YannickR26/ESP-Power-Monitoring/Software/src/HttpServer.cpp

#include <littleFS.h>
#include <ESP8266mDNS.h>
#include <ESP8266HTTPUpdateServer.h>

// You can update by 'curl -F "image=@firmware.bin" ESP_Monitoring.local/'

#include "WiFiManager.h"
#include "HttpServer.h"
#include "ATM90E32.h"
#include "Logger.h"
#include "Mqtt.h"

/********************************************************/
/******************** Public Method *********************/
/********************************************************/

HttpServer::HttpServer()
    : _webServer(80), _httpUpdater(true)
{
}

HttpServer::~HttpServer()
{
}

void HttpServer::setup(void)
{
  MDNS.begin(Configuration._hostname.c_str());
  MDNS.addService("http", "tcp", 80);

  _ftpServer.begin(Configuration._hostname, Configuration._hostname);
  MDNS.addService("ftp", "tcp", 21);

  _webServer.on("/restart", [&]() {
    _webServer.send(200, "text/plain", "ESP restart now !");
    delay(200);
    ESP.restart();
  });

  _webServer.on("/wifimanager", [&]() {
    _webServer.send(200, "text/plain", "Reset WifiManager configuration, restart now in AP mode...");
    delay(200);
    WiFiManager wifiManager;
    wifiManager.resetSettings();
    delay(200);
    ESP.restart();
  });

  _webServer.on("/config", HTTP_GET, HttpServer::getConfig);
  _webServer.on("/config", HTTP_POST, HttpServer::setConfig);
  _webServer.on("/status", HTTP_GET, HttpServer::getStatus);
  _webServer.on("/set", HttpServer::handleSet);

  _webServer.onNotFound(HttpServer::handleNotFound);

  _httpUpdater.setup(&_webServer, String("/update"));
  _webServer.begin();
}

void HttpServer::handle(void)
{
  _webServer.handleClient();
  MDNS.update();
  _ftpServer.handleFTP();
}

String HttpServer::getContentType(String filename)
{
  if (HTTPServer.webServer().hasArg("download"))
    return "application/octet-stream";
  else if (filename.endsWith(".htm"))
    return "text/html";
  else if (filename.endsWith(".html"))
    return "text/html";
  else if (filename.endsWith(".css"))
    return "text/css";
  else if (filename.endsWith(".js"))
    return "application/javascript";
  else if (filename.endsWith(".png"))
    return "image/png";
  else if (filename.endsWith(".gif"))
    return "image/gif";
  else if (filename.endsWith(".jpg"))
    return "image/jpeg";
  else if (filename.endsWith(".ico"))
    return "image/x-icon";
  else if (filename.endsWith(".xml"))
    return "text/xml";
  else if (filename.endsWith(".pdf"))
    return "application/x-pdf";
  else if (filename.endsWith(".zip"))
    return "application/x-zip";
  else if (filename.endsWith(".gz"))
    return "application/x-gzip";
  return "text/plain";
}

// send the right file to the client (if it exists)
bool HttpServer::handleFileRead(String path)
{
  Log.println("handleFileRead: " + path);
  if (path.endsWith("/"))
  {
    path += "index.html"; // If a folder is requested, send the index file
  }
  String contentType = HTTPServer.getContentType(path); // Get the MIME type
  String pathWithGz = path + ".gz";
  if (LittleFS.exists(pathWithGz) || LittleFS.exists(path))
  {                                                       // If the file exists, either as a compressed archive, or normal
    if (LittleFS.exists(pathWithGz))                      // If there's a compressed version available
      path += ".gz";                                      // Use the compressed verion
    File file = LittleFS.open(path, "r");                 // Open the file
    HTTPServer.webServer().streamFile(file, contentType); // Send it to the client
    file.close();                                         // Close the file again
    Log.println(String("\tSent file: ") + path);
    return true;
  }
  Log.println(String("\tFile Not Found: ") + path); // If the file doesn't exist, return false
  return false;
}

void HttpServer::handleNotFound()
{
  if (!HTTPServer.handleFileRead(HTTPServer.webServer().uri())) {
    String message = "File Not Found\n\n";
    message += "URI: ";
    message += HTTPServer.webServer().uri();
    message += "\nMethod: ";
    message += (HTTPServer.webServer().method() == HTTP_GET) ? "GET" : "POST";
    message += "\nArguments: ";
    message += HTTPServer.webServer().args();
    message += "\n";
    for (uint8_t i = 0; i < HTTPServer.webServer().args(); i++)
    {
      message += " " + HTTPServer.webServer().argName(i) + ": " + HTTPServer.webServer().arg(i) + "\n";
    }
    HTTPServer.webServer().send(404, "text/plain", message);
  }
}

void HttpServer::getStatus()
{
  Log.println("Send Status");
  
  DynamicJsonDocument doc(1024);
  doc.clear();

  doc["version"] = String(VERSION);
  doc["build"] = String(String(__DATE__) + " " + String(__TIME__));
  doc["relay"] = digitalRead(RELAY_PIN);

  JsonObject jsonLineA = doc.createNestedObject("lineA");
  metering line = Monitoring.getLineA();
  jsonLineA["voltage"] = line.voltage;
  jsonLineA["current"] = line.current;
  jsonLineA["power"] = line.power;
  jsonLineA["cosPhy"] = line.cosPhy;
  jsonLineA["conso"] = line.conso;

  JsonObject jsonLineB = doc.createNestedObject("lineB");
  line = Monitoring.getLineB();
  jsonLineB["voltage"] = line.voltage;
  jsonLineB["current"] = line.current;
  jsonLineB["power"] = line.power;
  jsonLineB["cosPhy"] = line.cosPhy;
  jsonLineB["conso"] = line.conso;

  JsonObject jsonLineC = doc.createNestedObject("lineC");
  line = Monitoring.getLineC();
  jsonLineC["voltage"] = line.voltage;
  jsonLineC["current"] = line.current;
  jsonLineC["power"] = line.power;
  jsonLineC["cosPhy"] = line.cosPhy;
  jsonLineC["conso"] = line.conso;

  // Send Status
  HTTPServer.sendJson(200, doc);
}

void HttpServer::getConfig() 
{
  Log.println("Send Configuration");
  
  DynamicJsonDocument doc(1024);
  Configuration.encodeToJson(doc);

  // Send Configuration
  HTTPServer.sendJson(200, doc);
}

void HttpServer::setConfig() 
{
  if (HTTPServer.webServer().hasArg("plain") == false) {
    Log.println("Error, no body received !");
    HTTPServer.webServer().sendHeader("Access-Control-Allow-Origin", "*");
    HTTPServer.webServer().send(404, "text/plain", "Body not received");
  }
  else {
    if (!Configuration.decodeJsonFromFile(HTTPServer.webServer().arg("plain").c_str())) {
      Log.println("Received new configuration !");
      HTTPServer.webServer().sendHeader("Access-Control-Allow-Origin", "*");
      Monitoring.setConsoLineA(Configuration._consoA);
      Monitoring.setConsoLineB(Configuration._consoB);
      Monitoring.setConsoLineC(Configuration._consoC);
      if (Configuration.saveConfig()) {
      // HTTPServer.webServer().send(200, "application/json", Configuration.encodeToJson());
        HTTPServer.webServer().send(200, "application/json", "{\"result\":true}");
      }
      else {
        HTTPServer.webServer().send(200, "application/json", "{\"result\":false}");
      }
    }
    else {
      Log.println("Error, parsing JSON !");
      HTTPServer.webServer().sendHeader("Access-Control-Allow-Origin", "*");
      HTTPServer.webServer().send(404, "text/plain", "Error with parsing JSON");
    }
  }
}

void HttpServer::handleSet()
{
  String message;
  for (uint8_t i = 0; i < HTTPServer.webServer().args(); ++i)
  {
    String name = HTTPServer.webServer().argName(i);
    String value = HTTPServer.webServer().arg(i).c_str();
    if (String(name) == "relay")
    {
      int status = value.toInt();
      digitalWrite(RELAY_PIN, status);
      Log.println(String("set relay to ") + String(status));
      MqttClient.publish(String("/relay"), String(status));
      message += "Set Relay to " + String(status) + "\n";
    }
    else if (String(name) == "timeIntervalUpdate")
    {
      int time = value.toInt();
      Log.println(String("set timeSendData to ") + String(time));
      Configuration._timeSendData = time;
      Configuration.saveConfig();
      MqttClient.publish(String("/timeIntervalUpdate"), String(Configuration._timeSendData));
      message += "Set time Send Data to " + String(time) + "\n";
    }
    else if (String(name) == "mode")
    {
      int mode = value.toInt();
      Log.println(String("set mode to ") + String(mode));
      Configuration._mode = mode;
      Configuration.saveConfig();
      MqttClient.publish(String("/mode"), String(Configuration._mode));
      message += "Set Mode to " + String(mode) + "\n";
    }
    else if (String(name) == "hostname")
    {
      String hostname = value;
      Log.println("Change hostname to " + hostname);
      Configuration._hostname = hostname;
      Configuration.saveConfig();
      message += "Set hostname to " + String(hostname) + "\n";
    }
    else if (String(name) == "consoA")
    {
      int conso = value.toInt();
      Log.println("Set conso A to " + String(conso));
      Monitoring.setConsoLineA(conso);
      message += "Set consoA to " + String(conso) + "\n";
    }
    else if (String(name) == "consoB")
    {
      int conso = value.toInt();
      Log.println("Set conso B to " + String(conso));
      Monitoring.setConsoLineB(conso);
      message += "Set consoB to " + String(conso) + "\n";
    }
    else if (String(name) == "consoC")
    {
      int conso = value.toInt();
      Log.println("Set conso C to " + String(conso));
      Monitoring.setConsoLineC(conso);
      message += "Set consoC to " + String(conso) + "\n";
    }
  }

  HTTPServer.webServer().sendHeader("Access-Control-Allow-Origin", "*");
  HTTPServer.webServer().send(200, "text/plain", message);
}

ESP8266WebServer &HttpServer::webServer()
{
  return _webServer;
}

/********************************************************/
/******************** Private Method ********************/
/********************************************************/

void HttpServer::sendJson(const uint16 code, JsonDocument &doc)
{
  WiFiClient client = HTTPServer.webServer().client();

  // Write Header
  client.print(F("HTTP/1.0 "));
  client.print(code);
  client.println(F(" OK"));
  client.println(F("Content-Type: application/json"));
  client.println(F("Access-Control-Allow-Origin: *"));
  client.print(F("Content-Length: "));
  client.println(measureJson(doc));
  client.println(F("Connection: close"));
  client.println();

  // Write JSON document
  serializeJson(doc, client);
}

#if !defined(NO_GLOBAL_INSTANCES)
HttpServer HTTPServer;
#endif
