YannickR26/ESP-Power-Monitoring/Software/src/Mqtt.h

#pragma once

#include <PubSubClient.h>

#include "settings.h"

class Mqtt
{
public:
	Mqtt();
	virtual ~Mqtt();

	void setup();
	void handle();
	void publish(String topic, String body);
	void log(String level, String str);
	void publishMonitoringData();
	bool isConnected() { return clientMqtt.connected(); }

private:
	void reconnect();
	void callback(char *topic, uint8_t *payload, unsigned int length);

	PubSubClient clientMqtt;
};

#if !defined(NO_GLOBAL_INSTANCES)
extern Mqtt MqttClient;
#endif
